maarten-pennings/SevenSegment-over-Serial/SSoS360x180.png

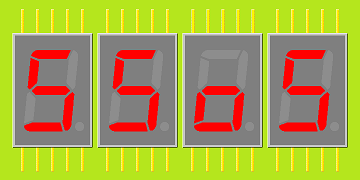
SSoS360x180.png
