maarten-pennings/SevenSegment-over-Serial/manual/ref.png

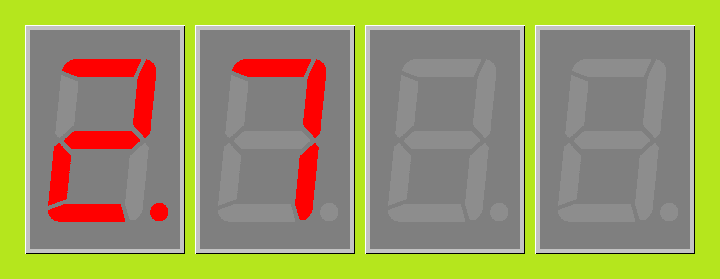
manual/ref.png
